mjmeans/kossel/Dasaki_ramps_enclosure_base_kossel.stl

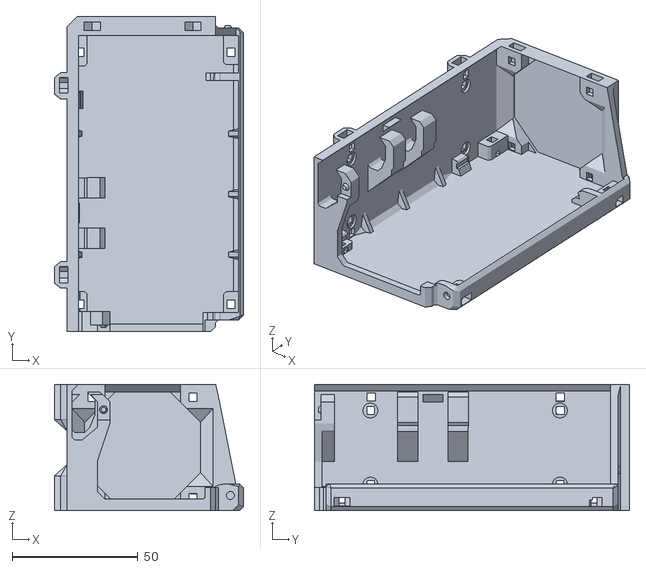
[picture p16: CAD file, 2016-08-30]
Dasaki_ramps_enclosure_base_kossel.stl
75.1 x 125.0 x 50.0
