mjmeans/kossel/dasaki_ramps_enclosure_cover_v2.stl

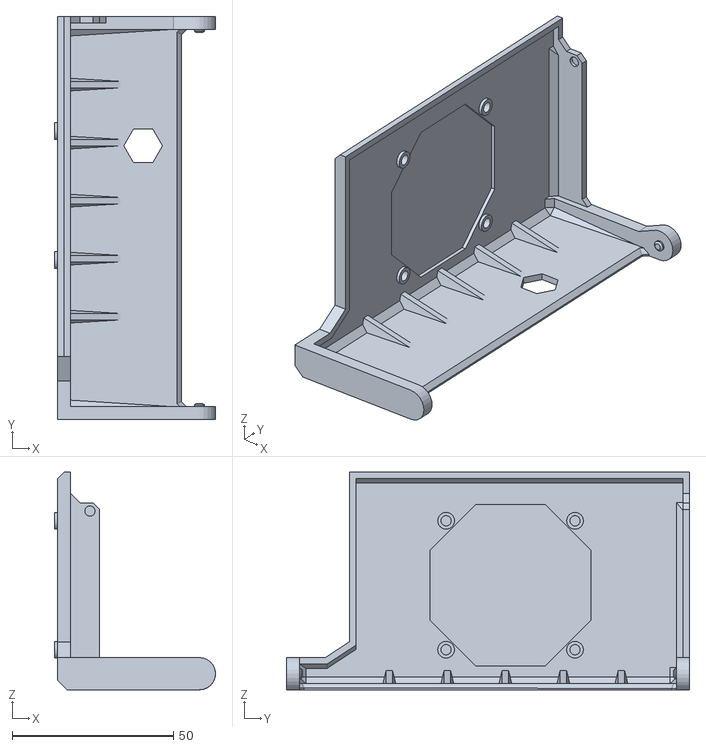
[picture p17: CAD file, 2016-08-30]
dasaki_ramps_enclosure_cover_v2.stl
50.0 x 125.0 x 67.6
