mjmeans/kossel/pscover_v2_with_aux_structs.stl

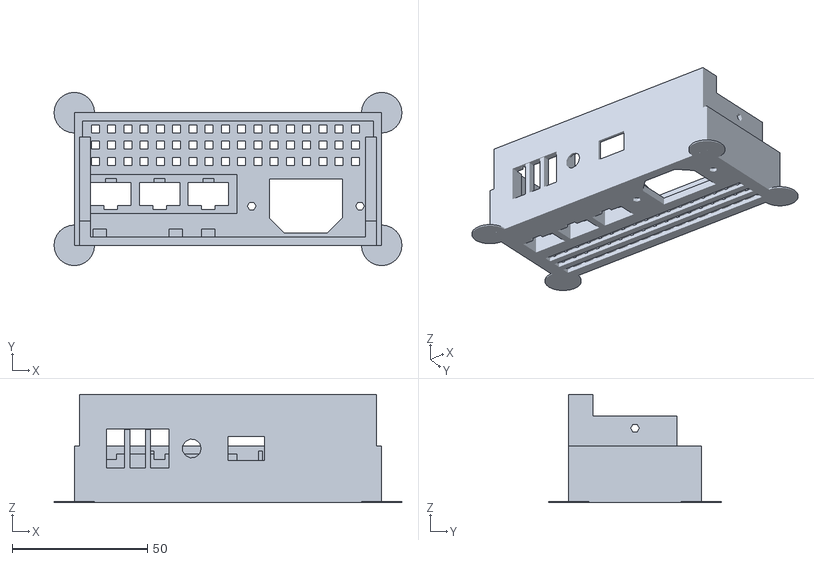
[picture p18: CAD file, 2016-08-30]
pscover_v2_with_aux_structs.stl
128.5 x 64.0 x 40.0
