mjmeans/kossel/3DR_Pablo_LCD_distance_cylinder.stl

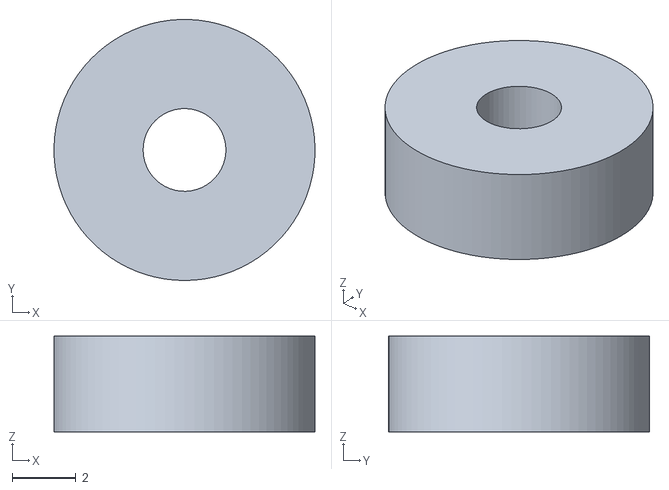
[picture p19: CAD file, 2016-08-30]
3DR_Pablo_LCD_distance_cylinder.stl
8.20 x 8.20 x 3.00
