mjmeans/kossel/3DR_Pablo_LCD_case_bottom.stl

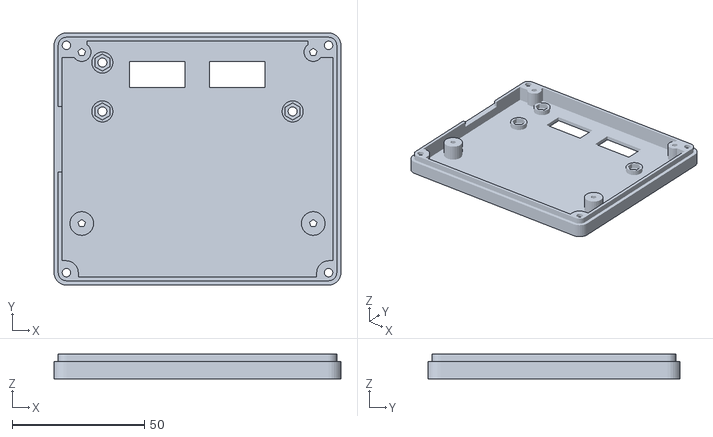
[picture p20: CAD file, 2016-08-30]
3DR_Pablo_LCD_case_bottom.stl
108.6 x 95.4 x 9.28
