mjmeans/kossel/riser.stl

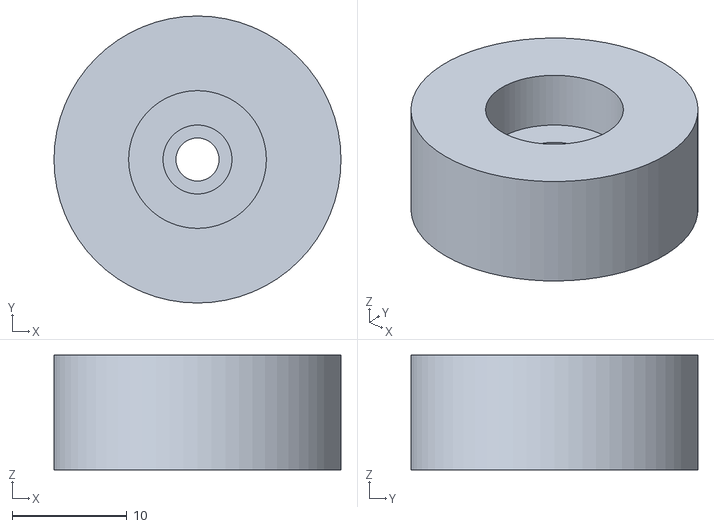
[picture p21: CAD file, 2016-08-30]
riser.stl
25.0 x 25.0 x 10.0
