mjmeans/kossel/3DR_Pablo_LCD_case_top.stl

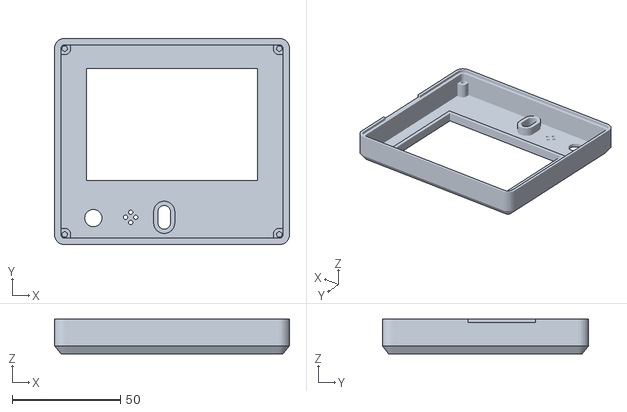
[picture p22: CAD file, 2016-08-30]
3DR_Pablo_LCD_case_top.stl
108.6 x 95.4 x 16.0
