mjmeans/kossel/Bearing-flanged.stl

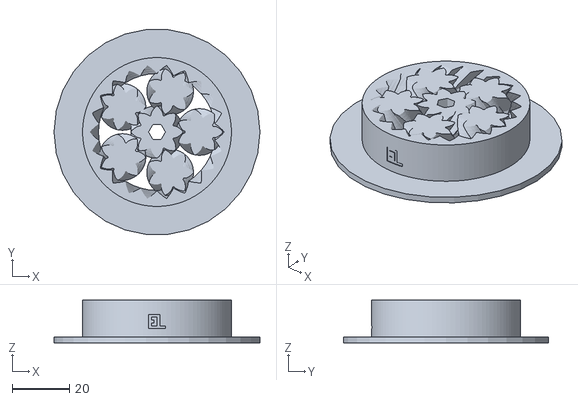
[picture p23: CAD file, 2016-08-30]
Bearing-flanged.stl
72.0 x 71.6 x 15.0
