mjmeans/kossel/spool_adapter_shim.stl

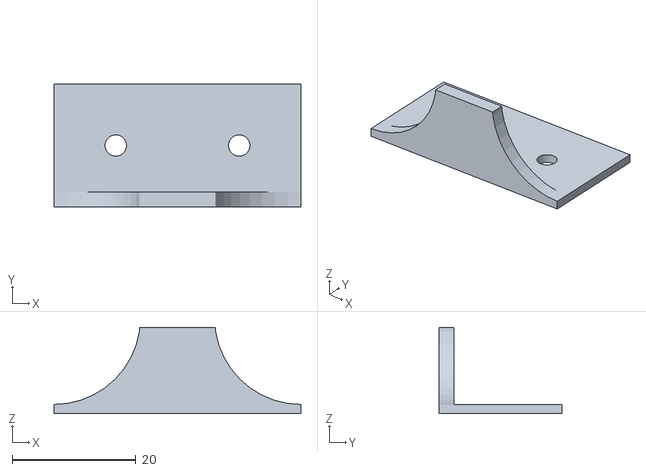
[picture p24: CAD file, 2016-08-30]
spool_adapter_shim.stl
40.0 x 20.0 x 14.0
