mjmeans/kossel/Kossel_Endstop_Mount.stl

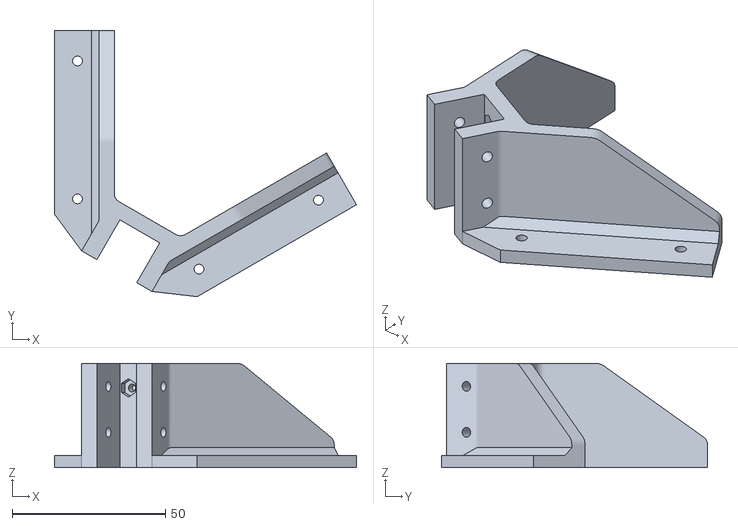
[picture p25: CAD file, 2016-08-30]
Kossel_Endstop_Mount.stl
98.5 x 86.9 x 34.0
