mjmeans/kossel/lcd_mount_bushing.stl

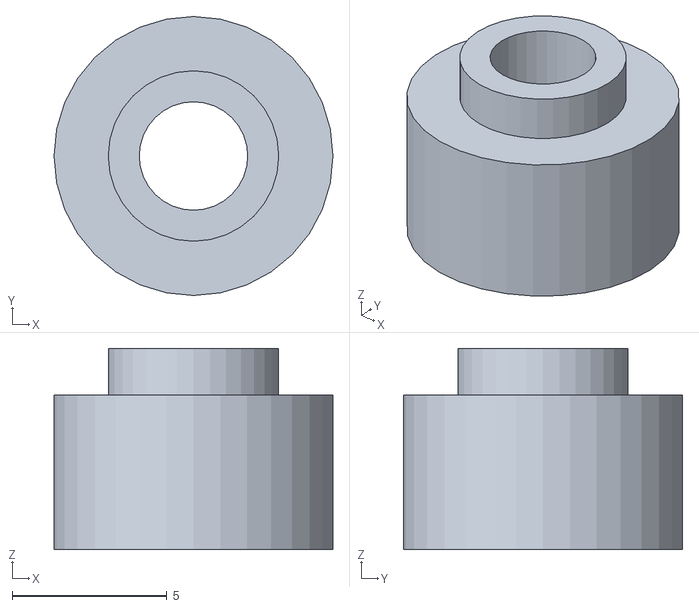
[picture p26: CAD file, 2016-08-30]
lcd_mount_bushing.stl
9.00 x 9.00 x 6.50
