mjmeans/kossel/new_endstop.stl

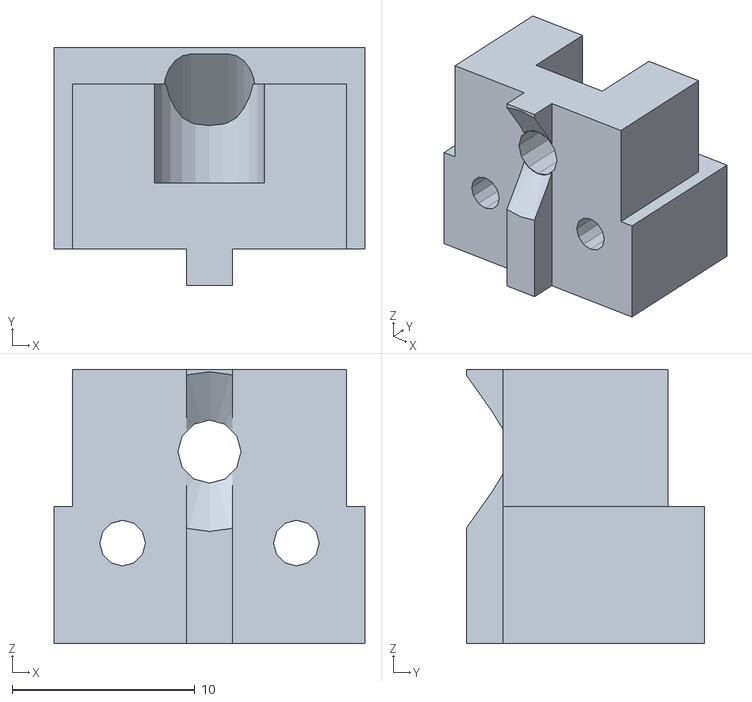
[picture p27: CAD file, 2016-08-30]
new_endstop.stl
17.0 x 13.0 x 15.0
