mjmeans/kossel/recirculating.stl

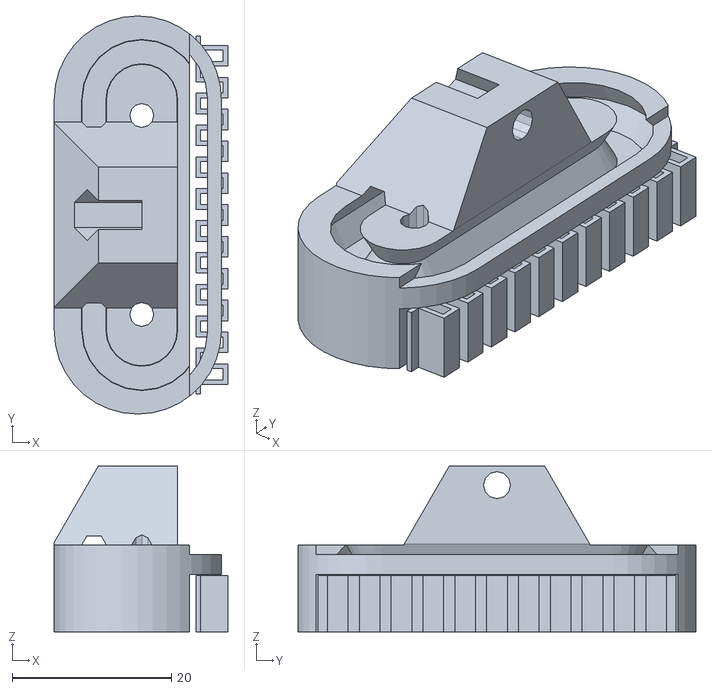
[picture p28: CAD file, 2016-08-30]
recirculating.stl
21.8 x 50.0 x 20.8
