mjmeans/kossel/Kossel_Cable_Tidy.stl

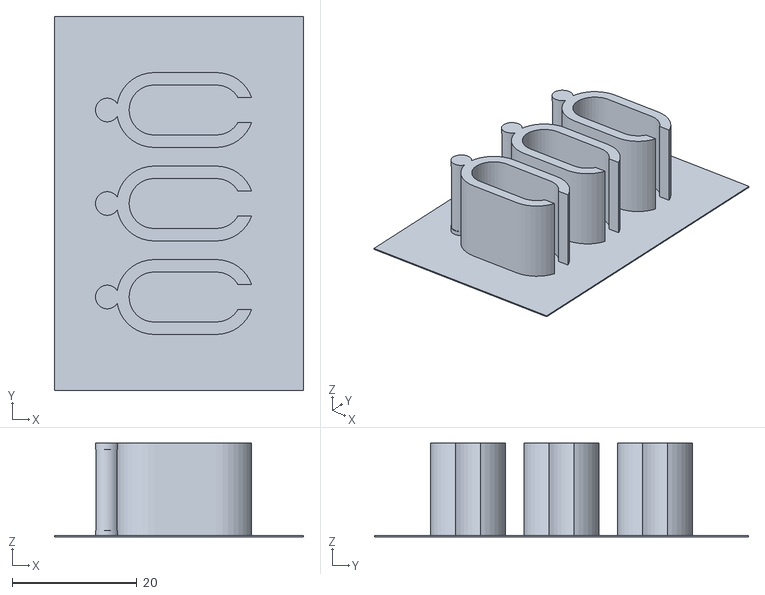
[picture p29: CAD file, 2016-08-30]
Kossel_Cable_Tidy.stl
40.0 x 60.0 x 15.0
