mjmeans/kossel/new_plate.stl

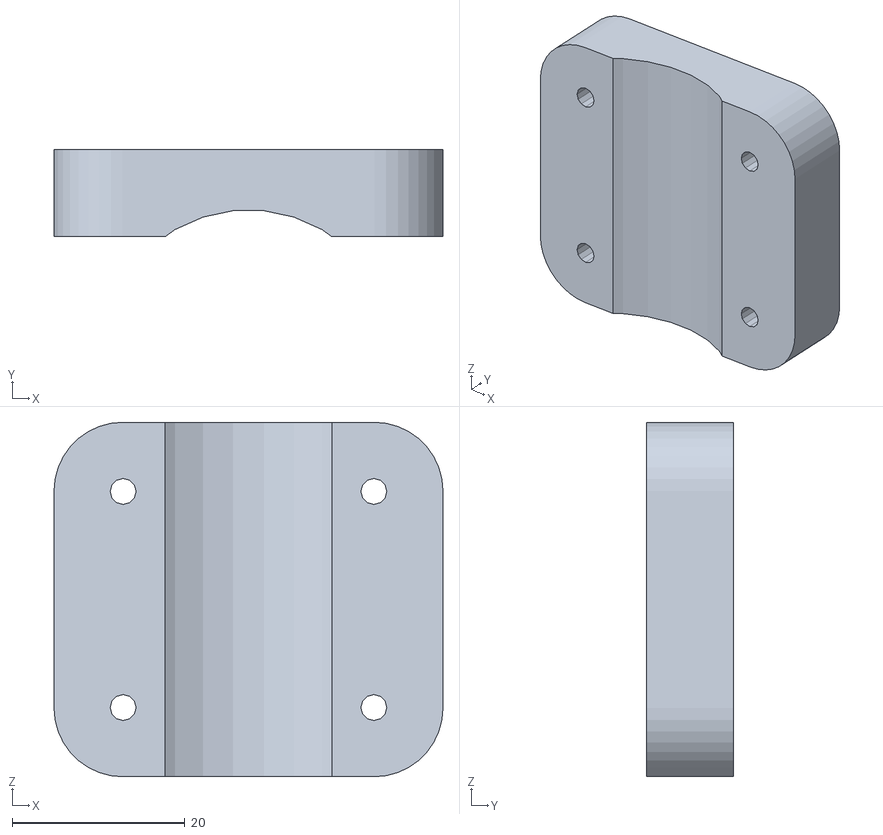
[picture p30: CAD file, 2016-08-30]
new_plate.stl
45.0 x 10.1 x 41.0
