mjmeans/kossel/3D_PlastX_reel_adapter.stl

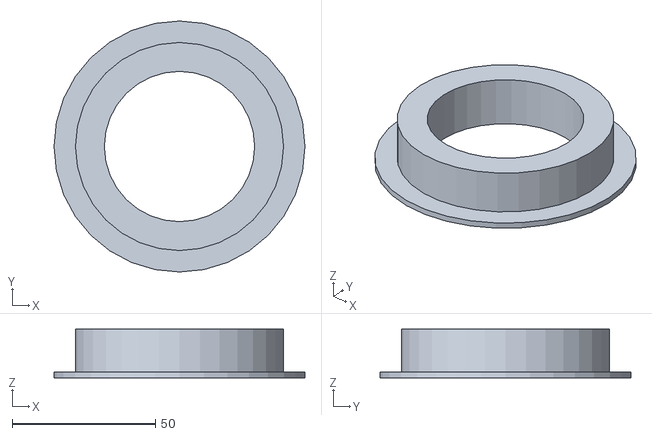
[picture p31: CAD file, 2016-08-30]
3D_PlastX_reel_adapter.stl
87.7 x 87.7 x 17.0
