mjmeans/kossel/B-struder_1515_90_plate.stl

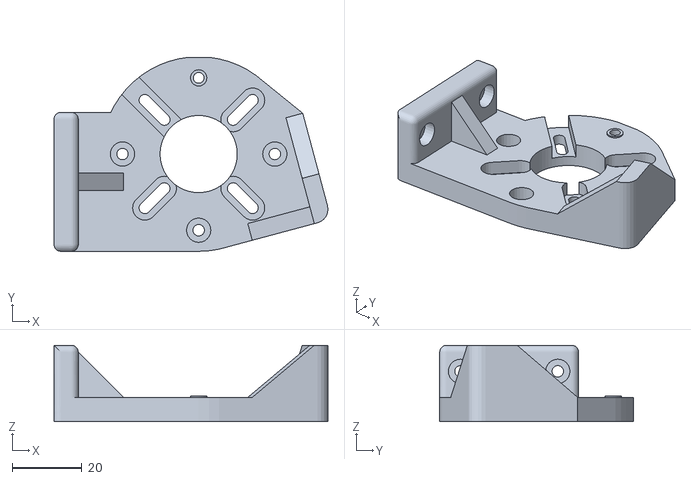
[picture p32: CAD file, 2016-08-30]
B-struder_1515_90_plate.stl
78.8 x 55.7 x 22.0
