mjmeans/kossel/framebrace_v2.stl

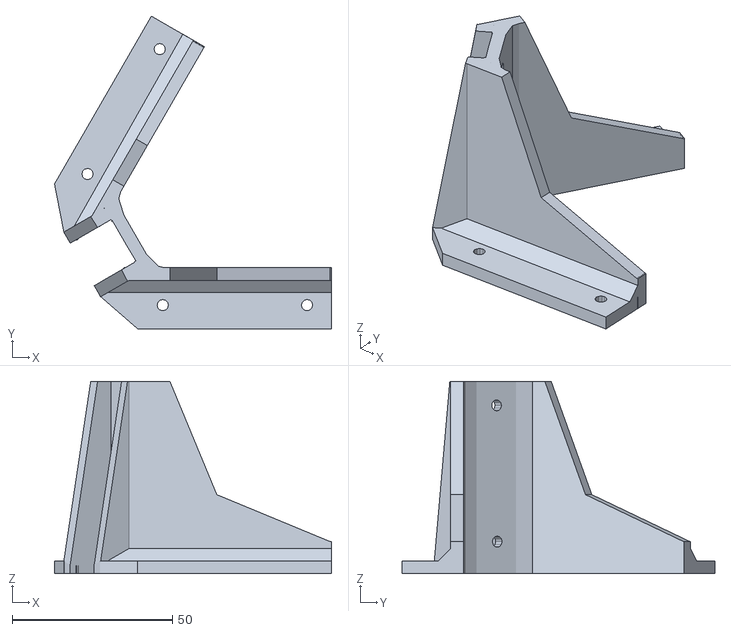
[picture p33: CAD file, 2016-08-30]
framebrace_v2.stl
86.4 x 97.5 x 60.0
