mjmeans/kossel/trimpot_cutout_cover.stl

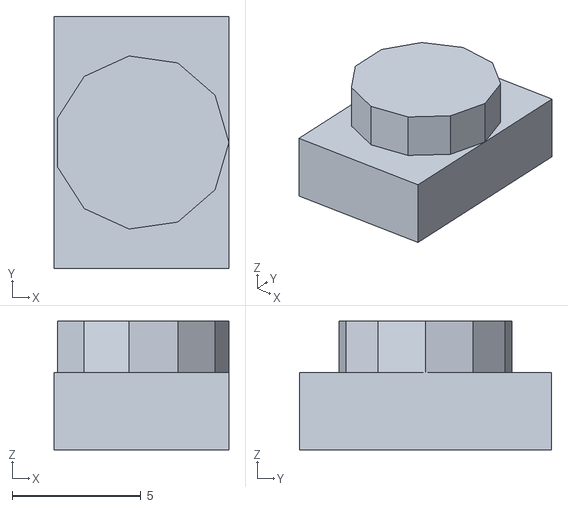
[picture p34: CAD file, 2016-08-30]
trimpot_cutout_cover.stl
6.80 x 9.80 x 5.00
