mjmeans/kossel/Filament_Guide.stl

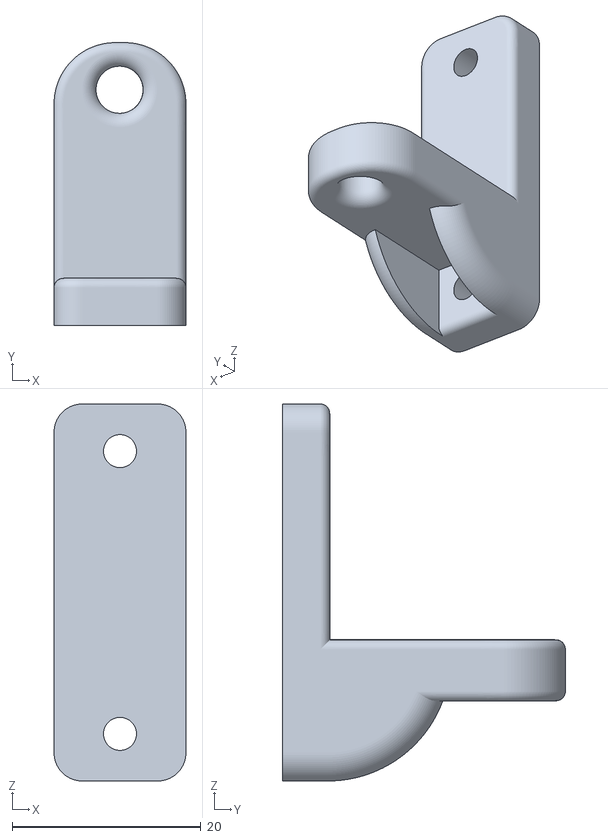
[picture p35: CAD file, 2016-08-30]
Filament_Guide.stl
14.0 x 30.0 x 40.0
