mjmeans/kossel/clip.stl

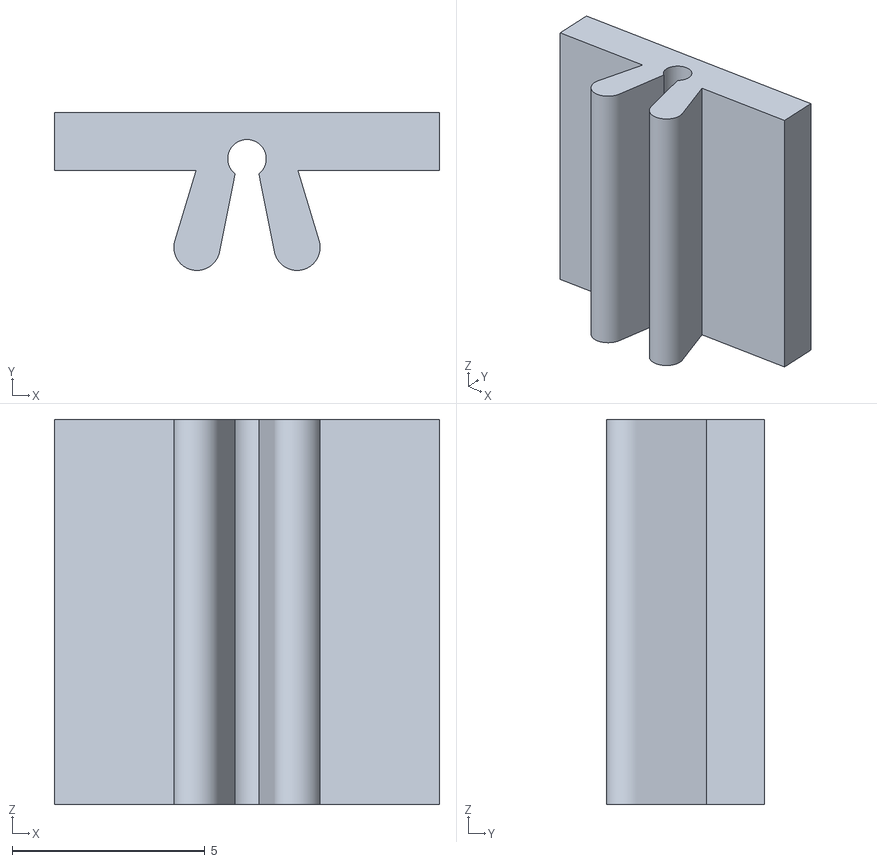
[picture p36: CAD file, 2016-08-30]
clip.stl
10.0 x 4.10 x 10.0
